joselogreira/nixie_clock/docs/assets/img/black-wall-in-close-up-image-3826435.jpg

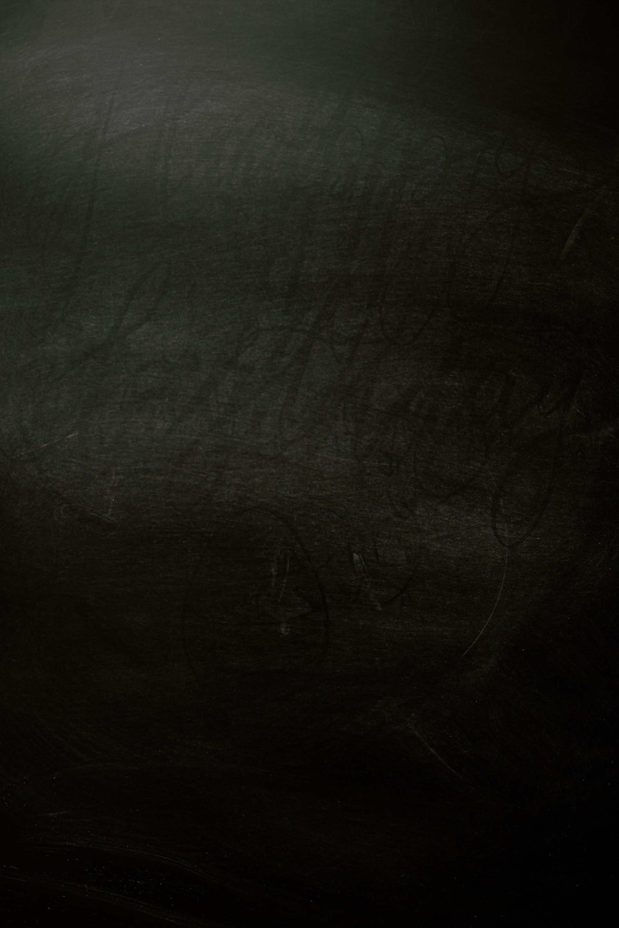
docs/assets/img/black-wall-in-close-up-image-3826435.jpg
