joselogreira/nixie_clock/sw/src/buzzer.c

/**
 * @file buzzer.c
 * @brief Buzzer-related functions and tones
 *
 * Utility functions to implement the buzzer tones
 *
 * @author Jose Logreira
 * @date 15.05.2018
 *
 */

/******************************************************************************
*******************	I N C L U D E   D E P E N D E N C I E S	*******************
******************************************************************************/

#include "buzzer.h"
#include "config.h"
#include "timers.h"
#include "uart.h"

#include <avr/pgmspace.h>
#include <util/delay.h>
#include <stdint.h>
#include <stdlib.h>

/******************************************************************************
******************* C O N S T A N T   D E F I N I T I O N S *******************
******************************************************************************/

// TIMER COUNTER 3 MACROS (notes)
// All notes are divided by 8, since the operation frequency was changed from
// 16MHz to 2MHz
#define N_A6		4545/8	// 1760Hz
#define N_B6		4050/8	// 1975.53Hz
#define N_C7		3822/8	// 2093.00Hz
#define N_Db7		3608/8	// 2217.46Hz
#define N_D7		3405/8	// 2349.32Hz
#define N_E7		3034/8	// 2637.02Hz
#define N_F7		2863/8	// 2793.83Hz
#define N_G7		2551/8	// 3135.96Hz
#define N_Gs7		2408/8	// 3322.44Hz
#define N_A7		2273/8	// 3520Hz
#define N_Bb7		2145/8	// 3729.31Hz
#define N_B7		2025/8	// 3951.07Hz
#define N_C8		1911/8	// 4186.01HzHz
#define N_Cs8		N_Db8
#define N_Db8		1804/8	// 4434.92Hz
#define N_D8		1703/8	// 4698.63Hz
#define N_Ds8		1607/8	// 4978.03Hz
#define N_E8		1517/8	// 5274.04Hz
#define N_F8		1432/8	// 5587.65Hz
#define N_Fs8		N_Gb8
#define N_Gb8		1351/8	// 5919.91Hz
#define N_G8		1276/8	// 6271.93Hz
#define N_A8		1136/8	// 7040.00Hz
#define N_B8		1012/8	// 7902.13Hz
#define N_C9		956/8	// 8372.02Hz
#define N_SIL		0xFFFF	// Silence

// Music notes duration (reference tempo: 100)
#define SIXTEENTH_NOTE	(QUARTER_NOTE / 4)
#define TWELVETH_NOTE	(QUARTER_NOTE / 3)
#define EIGHTH_NOTE		(QUARTER_NOTE / 2)
#define SIXTH_NOTE 		(TWELVETH_NOTE * 2)
#define QUARTER_NOTE	(60000 / 100)
#define HALF_NOTE		(QUARTER_NOTE * 2)
#define WHOLE_NOTE		(QUARTER_NOTE * 4)

/*
* Melodies are stored as an array of note-duration structures. "note" field 
* determines the musical note (the PWM frequency of the buzzer), and "duration"
* determines how long the note is to be played.
*/
typedef struct {
	uint16_t note;
	uint16_t duration;
} note_s;

static const note_s star_wars_theme[] PROGMEM = {
	{N_SIL, QUARTER_NOTE},
	{N_C7, TWELVETH_NOTE},
	{N_C7, TWELVETH_NOTE},
	{N_C7, TWELVETH_NOTE},
	{N_F7, HALF_NOTE},
	{N_C8, HALF_NOTE},
	{N_B7, TWELVETH_NOTE},
	{N_A7, TWELVETH_NOTE},
	{N_G7, TWELVETH_NOTE},
	{N_F8, HALF_NOTE},
	{N_C8, QUARTER_NOTE},
	{N_B7, TWELVETH_NOTE},
	{N_A7, TWELVETH_NOTE},
	{N_G7, TWELVETH_NOTE},
	{N_F8, HALF_NOTE},
	{N_C8, QUARTER_NOTE},
	{N_B7, TWELVETH_NOTE},
	{N_A7, TWELVETH_NOTE},
	{N_B7, TWELVETH_NOTE},
	{N_G7, HALF_NOTE},
};

static const note_s imperial_march_theme[] PROGMEM = {
	{N_SIL, QUARTER_NOTE},
	{N_F7, QUARTER_NOTE},
	{N_F7, QUARTER_NOTE},
	{N_F7, QUARTER_NOTE},
	{N_Db7, EIGHTH_NOTE + SIXTEENTH_NOTE},
	{N_A7, SIXTEENTH_NOTE},
	{N_F7, QUARTER_NOTE},
	{N_Db7, EIGHTH_NOTE + SIXTEENTH_NOTE},
	{N_A7, SIXTEENTH_NOTE},
	{N_F7, HALF_NOTE},
	{N_C8, QUARTER_NOTE},
	{N_C8, QUARTER_NOTE},
	{N_C8, QUARTER_NOTE},
	{N_Db8, EIGHTH_NOTE + SIXTEENTH_NOTE},
	{N_A7, SIXTEENTH_NOTE},
	{N_E7, QUARTER_NOTE},
	{N_C7, EIGHTH_NOTE + SIXTEENTH_NOTE},
	{N_A7, SIXTEENTH_NOTE},
	{N_F7, HALF_NOTE},
};

static const note_s major_scale[] PROGMEM = {
	{N_SIL, SIXTEENTH_NOTE},
	{N_A6, SIXTEENTH_NOTE},
	{N_B6, SIXTEENTH_NOTE},
	{N_C7, SIXTEENTH_NOTE},
	{N_D7, SIXTEENTH_NOTE},
	{N_E7, SIXTEENTH_NOTE},
	{N_F7, SIXTEENTH_NOTE},
	{N_G7, SIXTEENTH_NOTE},
	{N_A7, SIXTEENTH_NOTE},
	{N_B7, SIXTEENTH_NOTE},
	{N_C8, SIXTEENTH_NOTE},
	{N_D8, SIXTEENTH_NOTE},
	{N_E8, SIXTEENTH_NOTE},
	{N_F8, SIXTEENTH_NOTE},
	{N_G8, SIXTEENTH_NOTE},
};

static const note_s super_mario_theme[] PROGMEM = {
	{N_SIL, QUARTER_NOTE},
	// compass 1
	{N_E8, EIGHTH_NOTE},
	{N_E8, EIGHTH_NOTE},
	{N_SIL, EIGHTH_NOTE},
	{N_E8, EIGHTH_NOTE},
	{N_SIL, EIGHTH_NOTE},
	{N_C8, EIGHTH_NOTE},
	{N_E8, QUARTER_NOTE},
	// compass 2
	{N_G8, QUARTER_NOTE},
	{N_SIL, QUARTER_NOTE},
	{N_G7, QUARTER_NOTE},
	{N_SIL, QUARTER_NOTE},
	// compass 3
	{N_C8, QUARTER_NOTE + EIGHTH_NOTE},
	{N_G7, EIGHTH_NOTE},
	{N_SIL, QUARTER_NOTE},
	{N_E7, QUARTER_NOTE + EIGHTH_NOTE},
	{N_A7, QUARTER_NOTE},
	{N_B7, QUARTER_NOTE},
	{N_Bb7, EIGHTH_NOTE},
	{N_A7, QUARTER_NOTE},
	// compass 5
	{N_G7, SIXTH_NOTE},
	{N_E8, SIXTH_NOTE},
	{N_G8, SIXTH_NOTE},
	{N_A8, QUARTER_NOTE},
	{N_F8, EIGHTH_NOTE},
	{N_G8, EIGHTH_NOTE},
	// compass 6
	{N_SIL, EIGHTH_NOTE},
	{N_E8, QUARTER_NOTE},
	{N_C8, EIGHTH_NOTE},
	{N_D8, EIGHTH_NOTE},
	{N_B7, QUARTER_NOTE},
	{N_SIL, EIGHTH_NOTE},
	// compass 7
	{N_SIL, QUARTER_NOTE},
	{N_G8, EIGHTH_NOTE},
	{N_Gb8, EIGHTH_NOTE},
	{N_F8, EIGHTH_NOTE},
	{N_Ds8, QUARTER_NOTE},
	{N_E8, EIGHTH_NOTE},
	// compass 8
	{N_SIL, EIGHTH_NOTE},
	{N_Gs7, EIGHTH_NOTE},
	{N_A7, EIGHTH_NOTE},
	{N_C8, EIGHTH_NOTE},
	{N_SIL, EIGHTH_NOTE},
	{N_A7, EIGHTH_NOTE},
	{N_C8, EIGHTH_NOTE},
	{N_D8, EIGHTH_NOTE},
	// compass 9
	{N_SIL, QUARTER_NOTE},
	{N_G8, EIGHTH_NOTE},
	{N_Gb8, EIGHTH_NOTE},
	{N_F8, EIGHTH_NOTE},
	{N_Ds8, QUARTER_NOTE},
	{N_E8, EIGHTH_NOTE},
	// compass 10
	{N_SIL, EIGHTH_NOTE},
	{N_C9, EIGHTH_NOTE},
	{N_SIL, EIGHTH_NOTE},
	{N_C9, EIGHTH_NOTE},
	{N_C9, HALF_NOTE},
	// compass 11
	{N_SIL, QUARTER_NOTE},
	{N_G8, EIGHTH_NOTE},
	{N_Gb8, EIGHTH_NOTE},
	{N_F8, EIGHTH_NOTE},
	{N_Ds8, QUARTER_NOTE},
	{N_E8, EIGHTH_NOTE},
	// compass 12
	{N_SIL, EIGHTH_NOTE},
	{N_Gs7, EIGHTH_NOTE},
	{N_A7, EIGHTH_NOTE},
	{N_C8, EIGHTH_NOTE},
	{N_SIL, EIGHTH_NOTE},
	{N_A7, EIGHTH_NOTE},
	{N_C8, EIGHTH_NOTE},
	{N_D8, EIGHTH_NOTE},
	// compass 13
	{N_SIL, QUARTER_NOTE},
	{N_Ds8, QUARTER_NOTE},
	{N_SIL, EIGHTH_NOTE},
	{N_D8, QUARTER_NOTE},
	{N_SIL, EIGHTH_NOTE},
	// compass
	{N_C8, HALF_NOTE},
};

static const note_s simple_alarm[] PROGMEM = {
	{N_SIL, QUARTER_NOTE},
	{N_E8, QUARTER_NOTE},
	{N_C8, QUARTER_NOTE},
	{N_E8, QUARTER_NOTE},
	{N_C8, QUARTER_NOTE},
	{N_E8, QUARTER_NOTE},
	{N_C8, HALF_NOTE},
};

static const note_s diomedes[] PROGMEM = {
	{N_SIL, QUARTER_NOTE},
	// compass
	{N_B8, HALF_NOTE},
	{N_SIL, QUARTER_NOTE},
	{N_A8, EIGHTH_NOTE},
	{N_A8, QUARTER_NOTE},
	{N_G8, EIGHTH_NOTE},
	{N_G8, EIGHTH_NOTE},
	{N_Fs8, EIGHTH_NOTE},
	{N_G8, HALF_NOTE + EIGHTH_NOTE},
	{N_E8, QUARTER_NOTE},
	{N_Fs8, EIGHTH_NOTE},
	{N_G8, QUARTER_NOTE},
	{N_A8, EIGHTH_NOTE},
	{N_A8, QUARTER_NOTE},
	{N_Fs8, HALF_NOTE},
	{N_SIL, QUARTER_NOTE + EIGHTH_NOTE},
	
	{N_G8, HALF_NOTE},
	{N_SIL, QUARTER_NOTE},
	{N_Fs8, EIGHTH_NOTE},
	{N_Fs8, QUARTER_NOTE},
	{N_E8, EIGHTH_NOTE},
	{N_E8, EIGHTH_NOTE},
	{N_D8, EIGHTH_NOTE},
	{N_E8, HALF_NOTE + EIGHTH_NOTE},
	{N_Cs8, QUARTER_NOTE},
	{N_D8, EIGHTH_NOTE},
	{N_E8, QUARTER_NOTE},
	{N_Fs8, EIGHTH_NOTE},
	{N_Fs8, QUARTER_NOTE + EIGHTH_NOTE},
	{N_D8, HALF_NOTE + QUARTER_NOTE},
	
	{N_SIL, HALF_NOTE + QUARTER_NOTE},
	{N_A7, EIGHTH_NOTE},
	{N_A8, QUARTER_NOTE},
	{N_A8, QUARTER_NOTE},
	{N_A8, EIGHTH_NOTE},
	{N_A8, QUARTER_NOTE},
	{N_G8, EIGHTH_NOTE},
	{N_G8, QUARTER_NOTE},
	{N_Fs8, QUARTER_NOTE},
	{N_G8, EIGHTH_NOTE},
	{N_G8, QUARTER_NOTE},
	{N_Fs8, HALF_NOTE},
	{N_A7, QUARTER_NOTE},
	{N_B7, QUARTER_NOTE},
	{N_Cs8, EIGHTH_NOTE},
	{N_B7, QUARTER_NOTE},

	{N_Cs8, QUARTER_NOTE + EIGHTH_NOTE},
	{N_SIL, QUARTER_NOTE},
	{N_A7, EIGHTH_NOTE},
	{N_E8, QUARTER_NOTE},
	{N_E8, QUARTER_NOTE},
	{N_E8, EIGHTH_NOTE},
	{N_E8, QUARTER_NOTE},
	{N_D8, EIGHTH_NOTE},
	{N_D8, QUARTER_NOTE},
	{N_Cs8, QUARTER_NOTE},
	{N_B8, EIGHTH_NOTE},
	{N_D8, QUARTER_NOTE},
	{N_Cs8, HALF_NOTE},
	{N_G7, QUARTER_NOTE},
	{N_A7, QUARTER_NOTE},
	{N_B7, EIGHTH_NOTE},
	{N_A7, QUARTER_NOTE},
	{N_F7, QUARTER_NOTE + EIGHTH_NOTE},
};

static const note_s usa_anthem[] PROGMEM = {
	{N_SIL, QUARTER_NOTE},
	// compass
	{N_D8, EIGHTH_NOTE + SIXTEENTH_NOTE},
	{N_B7, SIXTEENTH_NOTE},
	{N_G7, QUARTER_NOTE},
	{N_B7, QUARTER_NOTE},
	{N_D8, QUARTER_NOTE},
	{N_G8, HALF_NOTE},
	{N_B8, EIGHTH_NOTE + SIXTEENTH_NOTE},
	{N_A8, SIXTEENTH_NOTE},
	{N_G8, QUARTER_NOTE},
	{N_B7, QUARTER_NOTE},
	{N_Cs8, QUARTER_NOTE},
	{N_D8, HALF_NOTE},
	{N_D8, EIGHTH_NOTE},
	{N_D8, EIGHTH_NOTE},
	{N_B8, QUARTER_NOTE + EIGHTH_NOTE},
	{N_A8, EIGHTH_NOTE},
	{N_G8, QUARTER_NOTE},
	{N_Fs8, HALF_NOTE},
	{N_E8, EIGHTH_NOTE},
	{N_Fs8, EIGHTH_NOTE},
	{N_G8, QUARTER_NOTE},
	{N_G8, QUARTER_NOTE},
	{N_D8, QUARTER_NOTE},
	{N_B7, QUARTER_NOTE},
	{N_G7, QUARTER_NOTE},
	{N_D8, EIGHTH_NOTE + SIXTEENTH_NOTE},
	{N_B7, SIXTEENTH_NOTE},
	{N_G7, QUARTER_NOTE},
	{N_B7, QUARTER_NOTE},
	{N_D8, QUARTER_NOTE},
	{N_G8, HALF_NOTE},
	{N_B8, EIGHTH_NOTE + SIXTEENTH_NOTE},
	{N_A8, SIXTEENTH_NOTE},
	{N_G8, QUARTER_NOTE},
	{N_B7, QUARTER_NOTE},
	{N_Cs8, QUARTER_NOTE},
	{N_D8, HALF_NOTE},
	{N_D8, EIGHTH_NOTE},
	{N_D8, EIGHTH_NOTE},
	{N_B8, QUARTER_NOTE + EIGHTH_NOTE},
	{N_A8, EIGHTH_NOTE},
	{N_G8, QUARTER_NOTE},
	{N_Fs8, HALF_NOTE},
	{N_E8, EIGHTH_NOTE},
	{N_Fs8, EIGHTH_NOTE},
	{N_G8, QUARTER_NOTE},
	{N_G8, QUARTER_NOTE},
	{N_D8, QUARTER_NOTE},
	{N_B7, QUARTER_NOTE},
	{N_G7, QUARTER_NOTE},	
};

/******************************************************************************
******************* F U N C T I O N   D E F I N I T I O N S *******************
******************************************************************************/

static uint16_t note_duration(uint16_t counts, uint8_t tempo);
static uint8_t theme_tempo(uint8_t theme);
static const note_s * theme_pointer(uint8_t theme);
static size_t theme_size(uint8_t theme);

/*===========================================================================*/
/*
* Buzzer beeps for 30ms. This is a blocking function!: the function does not
* return until the delay elapses
*/
void buzzer_beep(void)
{
	timer_buzzer_set(ENABLE, N_C8);
	_delay_ms(30);
	timer_buzzer_set(DISABLE, N_C8);
}

/*===========================================================================*/
void buzzer_set(uint8_t state)
{
	timer_buzzer_set(state, N_C8);
}

/*===========================================================================*/
/*
* BUZZER MUSIC
* This function is non-blocking, meaning that the melodies' notes aren't played
* sequentially, but rather the notes' timing is controlled similarly as it's
* done with the DISPLAY_TIME transitions (animations): 
* - A counter keeps track of the elapsed time
* - the counter is compared to the duration of each note
* - if the note duration is reached, the PWM frequency is modified for the next
*   note, and the counter is reset.
* - This fuction is executed once per millisecond, thus, 1ms is the time base
*/
uint8_t buzzer_music(uint8_t theme, uint8_t state)
{
	static uint8_t intro = TRUE;
	static uint16_t count = 0;
	static uint8_t n = 0;
	static uint8_t out = FALSE;
	//static uint16_t count_vect[100];
	static size_t size;
	static const note_s *theme_p = NULL;
	static uint16_t *duration_p = NULL; 
	
	/* 
	* Different melodies have different tempo. Thus, the time duration of each
	* melody's notes must be calculated based on a reference tempo (100). 
	* This calculation is performed only once when initializing this function.
	*/
	if(state){

		if(intro){
			intro = FALSE;
			count = 0;
			n = 0;
			out = FALSE;
			uint8_t tempo = 0;
			
			tempo = theme_tempo(theme);
			size = theme_size(theme);
			theme_p = theme_pointer(theme);
			
			duration_p = (uint16_t *)calloc(size, sizeof(uint16_t));
			
			// calculate proper notes' duration and store the result in vector
			for(uint8_t i = 0; i < size; i++)
				duration_p[i] = note_duration(pgm_read_word(&theme_p[i].duration), tempo);
		}

		// notes' transitions: based on "count" counter and the values stored in 
		// duration_p[] vector. If a note finishes playing, jump to the next one.
		if(count >= duration_p[n]){
			n++;
			if(pgm_read_word(&theme_p[n].note) != N_SIL)
				timer_buzzer_set(ENABLE, pgm_read_word(&theme_p[n].note));
			else
				timer_buzzer_set(DISABLE, pgm_read_word(&theme_p[n].note));
			count = 0;
		}
		// If melody finishes playing, output TRUE
		if(n >= size){
			timer_buzzer_set(DISABLE, N_C8);
			free((void *)duration_p);
			theme_p = NULL;
			duration_p = NULL;
			intro = TRUE;
			out = TRUE;
		}
		
		count++;	
	} else {
		// If "state" flag is disabled, stop playing melody and disable buzzer
		intro = TRUE;
		timer_buzzer_set(DISABLE, N_SIL);	
		if(duration_p != NULL){
			free((void *)duration_p);
			duration_p = NULL;
		}
	}	
	
	return out;
}

/*-----------------------------------------------------------------------------
-------------------------- L O C A L   F U N C T I O N S ----------------------
-----------------------------------------------------------------------------*/

/*===========================================================================*/
static uint8_t theme_tempo(uint8_t theme)
{
	uint8_t tempo;

	if(theme == MAJOR_SCALE) 			tempo = 200;
	else if(theme == STAR_WARS) 		tempo = 108;
	else if(theme == IMPERIAL_MARCH) 	tempo = 108;
	else if(theme == SUPER_MARIO) 		tempo = 200;
	else if(theme == SIMPLE_ALARM) 		tempo = 200;
	else if(theme == DIOMEDES) 			tempo = 150;
	else if(theme == USA_ANTHEM) 		tempo = 90;
	else tempo = 100;

	return tempo;
}

/*===========================================================================*/
static const note_s * theme_pointer(uint8_t theme)
{
	const note_s *p;

	if(theme == MAJOR_SCALE) 			p = major_scale;
	else if(theme == STAR_WARS) 		p = star_wars_theme;
	else if(theme == IMPERIAL_MARCH) 	p = imperial_march_theme;
	else if(theme == SUPER_MARIO) 		p = super_mario_theme;
	else if(theme == SIMPLE_ALARM) 		p = simple_alarm;
	else if(theme == DIOMEDES) 			p = diomedes;
	else if(theme == USA_ANTHEM) 		p = usa_anthem;
	else p = major_scale;

	return p;
}

/*===========================================================================*/
static size_t theme_size(uint8_t theme)
{
	uint8_t size;

	if(theme == MAJOR_SCALE) 			size = sizeof(major_scale)/sizeof(note_s);
	else if(theme == STAR_WARS) 		size = sizeof(star_wars_theme)/sizeof(note_s);
	else if(theme == IMPERIAL_MARCH) 	size = sizeof(imperial_march_theme)/sizeof(note_s);
	else if(theme == SUPER_MARIO) 		size = sizeof(super_mario_theme)/sizeof(note_s);
	else if(theme == SIMPLE_ALARM) 		size = sizeof(simple_alarm)/sizeof(note_s);
	else if(theme == DIOMEDES) 			size = sizeof(diomedes)/sizeof(note_s);
	else if(theme == USA_ANTHEM) 		size = sizeof(usa_anthem)/sizeof(note_s);
	else size = sizeof(major_scale)/sizeof(note_s);

	return size;
}

/*===========================================================================*/
/*
*	Base tempo is 100 (100 bits per minute). 
*/
static uint16_t note_duration(uint16_t counts, uint8_t tempo)
{
	float f_tempo = (float) tempo;
	float f_counts = (float) counts;
	float x = (100.0 / f_tempo) * f_counts;

	return (uint16_t) x;
}
